Palmr/gameboy-vga/rtl/gb-framebuffer.v

`default_nettype none

`include "vga.v"

module top(
    input wire CLK_16MHz,       // Oscillator input 16Mhz
    input wire scaling_x2,      // GB framebuffer scaling

    input [1:0] GB_DAT,         // GB pixel data 2 bit
    input wire GB_HSYNC,        // GB HSYNC
    input wire GB_VSYNC,        // GB VSYNC
    input wire GB_PX_CLK,       // GB pixel clock

    output [1:0] vga_r,         // VGA Red 2 bit
    output [1:0] vga_g,         // VGA Green 2 bit
    output [1:0] vga_b,         // VGA Blue 2 bit
    output wire vga_hs,         // H-sync pulse
    output wire vga_vs          // V-sync pulse
);
    parameter gb_h_pixels  = 160;
    parameter gb_v_pixels  = 144;

    // IO registers
    reg [1:0]   vga_r_r;    // VGA color registers R,G,B x 2 bit
    reg [1:0]   vga_g_r;
    reg [1:0]   vga_b_r;
    reg         vga_hs_r;   // H-SYNC register
    reg         vga_vs_r;   // V-SYNC register

    assign  vga_r   = vga_r_r;  // Assign the output signals for VGA to the VGA registers
    assign  vga_g   = vga_g_r;
    assign  vga_b   = vga_b_r;
    assign  vga_hs  = vga_hs_r;
    assign  vga_vs  = vga_vs_r;

    // VGA Pixel clock
    wire CLK_25MHz;             // 25MHz clock
    /**
    * PLL configuration
    *
    * This Verilog module was generated automatically
    * using the icepll tool from the IceStorm project.
    * Use at your own risk.
    *
    * Given input frequency:        16.000 MHz
    * Requested output frequency:   25.000 MHz
    * Achieved output frequency:    25.000 MHz
    */
    SB_PLL40_CORE #(
        .FEEDBACK_PATH("SIMPLE"),
        .DIVR(4'b0000),        // DIVR =  0
        .DIVF(7'b0110001),    // DIVF = 49
        .DIVQ(3'b101),        // DIVQ =  5
        .FILTER_RANGE(3'b001)    // FILTER_RANGE = 1
    ) uut (
        // .LOCK(locked),
        .RESETB(1'b1),
        .BYPASS(1'b0),
        .REFERENCECLK(CLK_16MHz),
        .PLLOUTCORE(CLK_25MHz)
    );

    // VGA module registers
    reg [9:0] vga_x;         // X coord
    reg [9:0] vga_y;         // Y coord
    reg vga_pixel_active;    // Display enable flag

    vga vga1(
        .clk(CLK_25MHz),
        .vga_pixel_active(vga_pixel_active),
        .vga_x(vga_x),
        .vga_y(vga_y),
        .vga_hsync(vga_hs_r),
        .vga_vsync(vga_vs_r)
    );

    // Framebuffer
    reg [14:0] write_addr = 0;
    reg [14:0] read_addr = 0;
    reg [1:0] in_pixel = 2'b10;
    reg [1:0] buffer_pixel;
    reg write_enable = 0;

    ram fb_gameboy (
        .din(GB_DAT),
        .write_en(write_enable), 
        .waddr(write_addr), 
        .wclkN(GB_PX_CLK), 
        .raddr(read_addr),
        .rclkN(CLK_25MHz), 
        .dout(buffer_pixel)
    );

    reg VSYNCED, VSANKED, PIXEL_SEEN, PIXEL_SEEN_RECENTLY;
    initial {VSYNCED, VSANKED, PIXEL_SEEN, PIXEL_SEEN_RECENTLY} = 4'b0000;

    // Data writes on negedge of GB_PX_CLK, increment address on posedge
    always @(posedge GB_PX_CLK)
    begin
        PIXEL_SEEN <= ~PIXEL_SEEN_RECENTLY;

        if (VSYNCED == ~VSANKED)
        begin
            write_addr <= 14'b0;
            write_enable <= 1;
            VSANKED <= VSYNCED;
        end
        else begin
            write_addr <= write_addr + 1;
        end
    end
    // // Reset pixel counter after 500us of no pixels seen
    reg [14:0] clock_counter;
    always @(posedge CLK_25MHz)
    begin
        if (clock_counter == 12500) begin
            clock_counter <= 0;
            // Every time the pixel clocks we set seen to inverse of seen_recently, if equal nothing seen since last countdown expiry
            if (PIXEL_SEEN == PIXEL_SEEN_RECENTLY) begin
                VSYNCED <= ~VSANKED;
            end
            else begin
                PIXEL_SEEN_RECENTLY <= ~PIXEL_SEEN_RECENTLY;
            end
        end
        else begin
            clock_counter <= clock_counter + 1;
        end
    end

    // Scaling 
    reg [1:0] scaling = 1 << scaling_x2;
    reg [8:0] scaled_gb_h_pixels = gb_h_pixels * scaling;
    reg [8:0] scaled_gb_v_pixels = gb_v_pixels * scaling;
    reg [7:0] offset_x = (640 / 2) - (scaled_gb_h_pixels / 2);
    reg [7:0] offset_y = (480 / 2) - (scaled_gb_v_pixels / 2);

    always @(posedge CLK_25MHz) begin
        if(vga_pixel_active == 1) begin
            if (
                vga_x >= offset_x && vga_x < offset_x + scaled_gb_h_pixels && 
                vga_y >= offset_y && vga_y < offset_y + scaled_gb_v_pixels
            ) begin
                decode_gb_to_rgb(buffer_pixel, vga_r_r, vga_g_r, vga_b_r);             

                if (scaling == 1) begin
                    read_addr <= read_addr + 1;
                end else if (scaling == 2) begin
                    read_addr <= read_addr + vga_x[0];
                end
            end
            else if (
                scaling == 2 && 
                vga_x == offset_x + scaled_gb_h_pixels && 
                vga_y >= offset_y && vga_y < offset_y + scaled_gb_v_pixels &&
                vga_y[0] == 0
            ) begin
                read_addr <= read_addr - gb_h_pixels;

                vga_r_r <= 0;
                vga_g_r <= 0;
                vga_b_r <= 0;
            end
            else if (
                vga_x == offset_x + scaled_gb_h_pixels && 
                vga_y == offset_y + scaled_gb_v_pixels
            ) begin
                read_addr <= 0;

                vga_r_r <= 0;
                vga_g_r <= 0;
                vga_b_r <= 0;
            end
            else begin
                vga_r_r <= 0;
                vga_g_r <= 0;
                vga_b_r <= 0;
            end
        end
        else begin  // When display is not enabled everything is black
            vga_r_r <= 0;
            vga_g_r <= 0;
            vga_b_r <= 0;
        end
    end

    task decode_gb_to_rgb (
        input  [1:0] data_in,
        output [1:0] data_out_r,
        output [1:0] data_out_g,
        output [1:0] data_out_b
    );
        begin
            data_out_r = ~data_in;
            data_out_g = ~data_in;
            data_out_b = ~data_in;
        end
    endtask

endmodule

module ram (
    din,
    write_en, 
    waddr, 
    wclkN, 
    raddr,
    rclkN, 
    dout
);
    parameter addr_width = 15;
    parameter data_width = 2;

    input [addr_width-1:0] waddr, raddr;
    input [data_width-1:0] din;
    input write_en, wclkN, rclkN;

    output reg [data_width-1:0] dout;

    reg [data_width-1:0] mem [(1<<addr_width)-1:0];
    initial $readmemb("empty-fb.bin", mem);

    always @(negedge wclkN)
    begin
        if (write_en)
            mem[waddr] <= din;
    end

    always @(negedge rclkN)
    begin
        dout <= mem[raddr];
    end
endmodule
